notchrisyoung/Human-Detecting-Lights/include/secrets.example.h

#pragma once
// Template for your local settings. Copy this file to include/secrets.h and
// fill it in; secrets.h is git-ignored so your Wi-Fi password stays off GitHub.

#define WIFI_SSID     "your-wifi-name"
#define WIFI_PASSWORD "your-wifi-password"

// The Kasa switch's name exactly as it appears in the Kasa app.
#define SWITCH_NAME   "Living Room Light"
